thebenheckshow/187-teensy-tinball-portable/pics/IMG_20150423_170455569.jpg

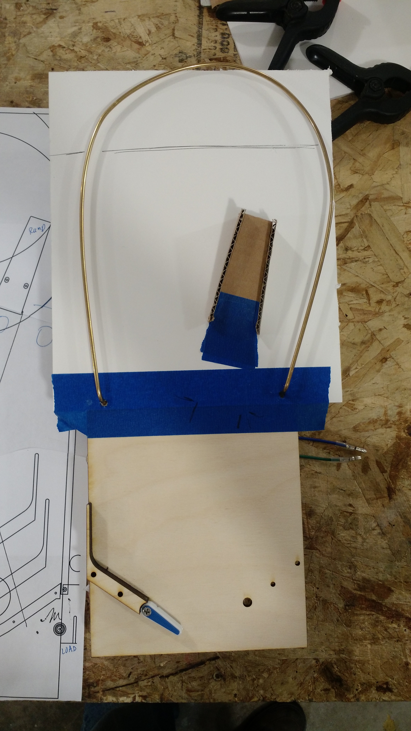
pics/IMG_20150423_170455569.jpg
