thebenheckshow/187-teensy-tinball-portable/pics/IMG_20150505_093643514.jpg

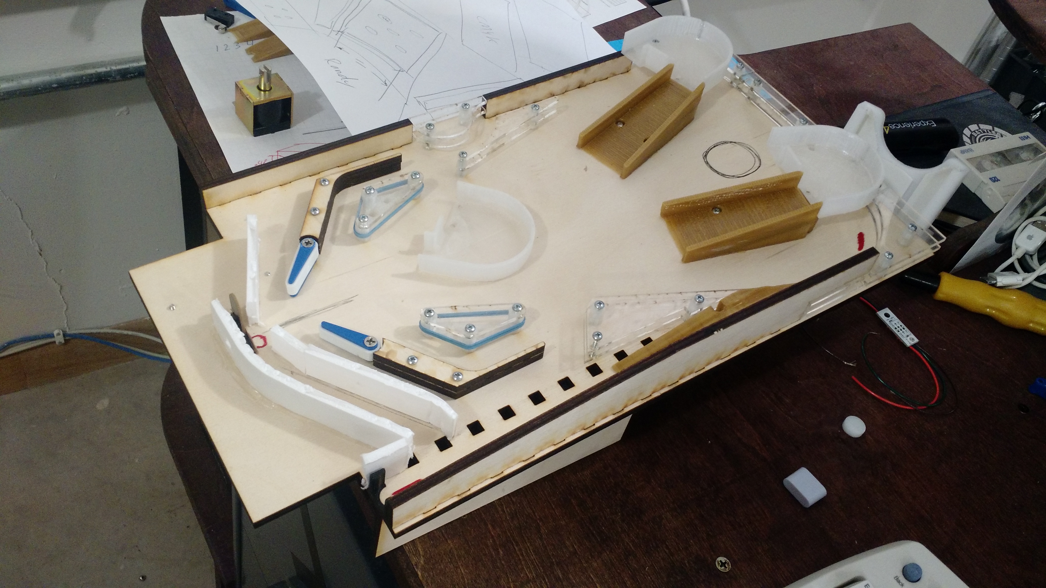
pics/IMG_20150505_093643514.jpg
