thebenheckshow/187-teensy-tinball-portable/pics/IMG_20150505_152138427.jpg

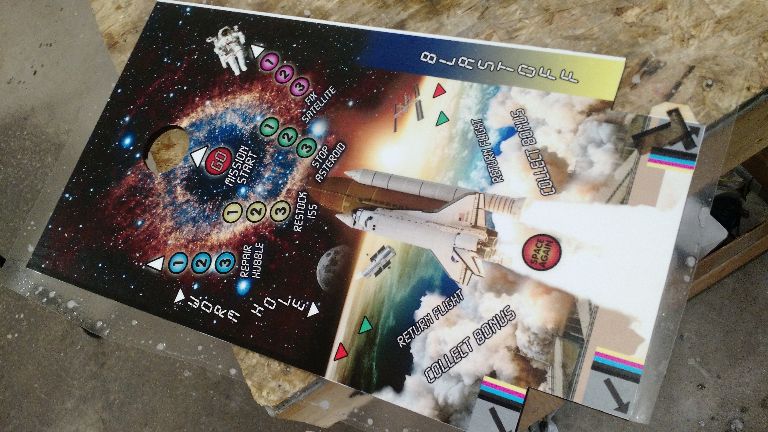
pics/IMG_20150505_152138427.jpg
