thebenheckshow/187-teensy-tinball-portable/pics/IMG_20150508_121546331.jpg

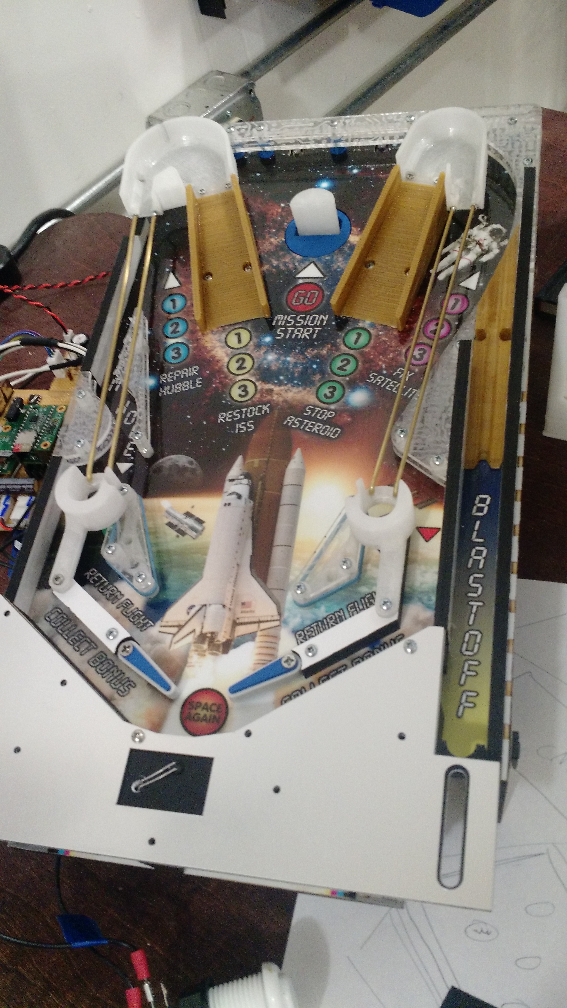
pics/IMG_20150508_121546331.jpg
