thebenheckshow/187-teensy-tinball-portable/pics/IMG_20150509_205021289.jpg

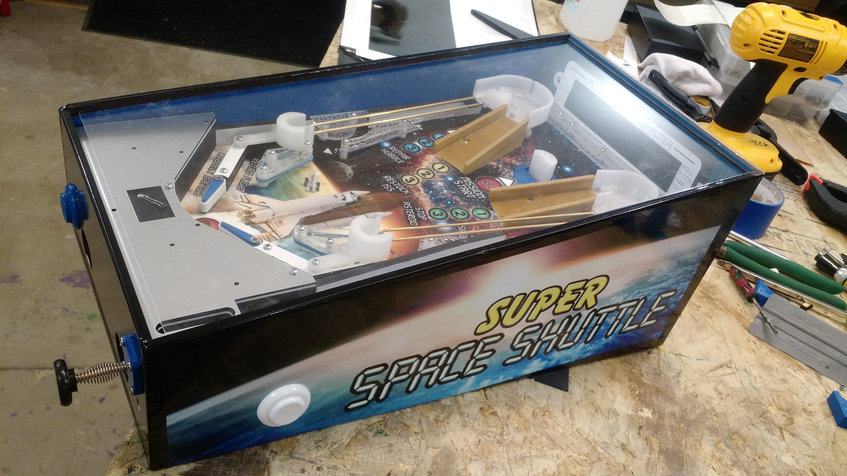
pics/IMG_20150509_205021289.jpg
