thebenheckshow/187-teensy-tinball-portable/pics/IMG_20150717_111414935.jpg

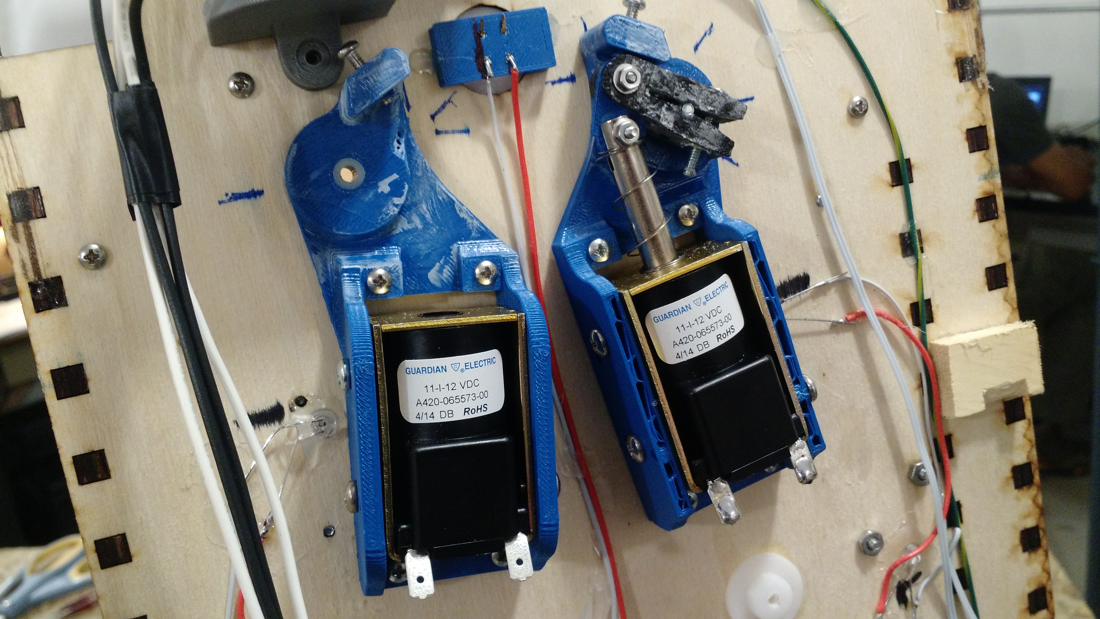
pics/IMG_20150717_111414935.jpg
