thebenheckshow/187-teensy-tinball-portable/3D parts/STL/Drop Target.stl

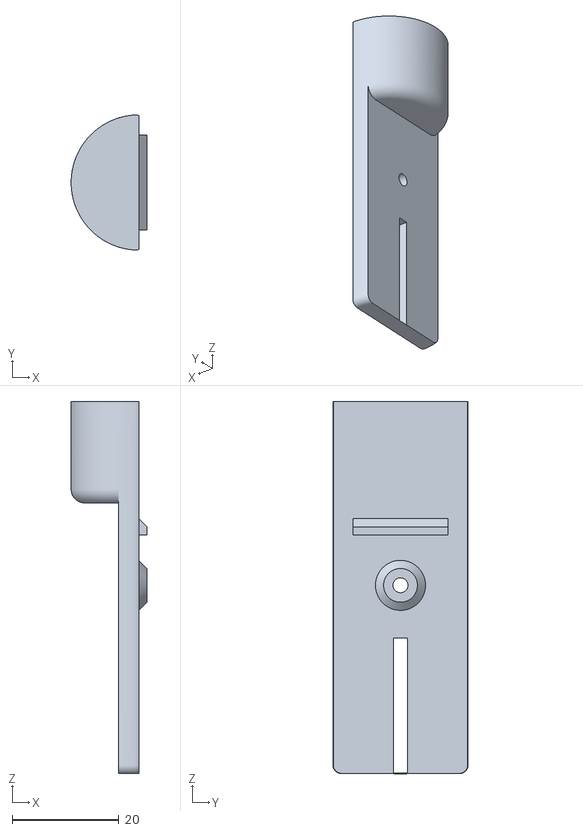
[picture p24: CAD file, 2015-11-03]
3D parts/STL/Drop Target.stl
14.2 x 25.4 x 69.8
