thebenheckshow/187-teensy-tinball-portable/3D parts/STL/Opto Mount 2.stl

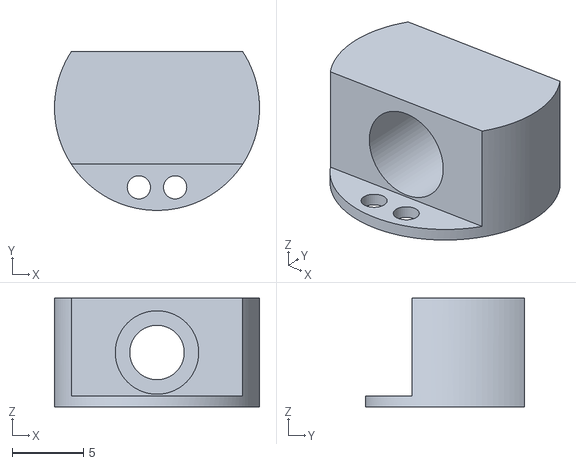
[picture p25: CAD file, 2015-11-03]
3D parts/STL/Opto Mount 2.stl
14.3 x 11.1 x 7.62
