thebenheckshow/187-teensy-tinball-portable/3D parts/STL/Shooter Tip.stl

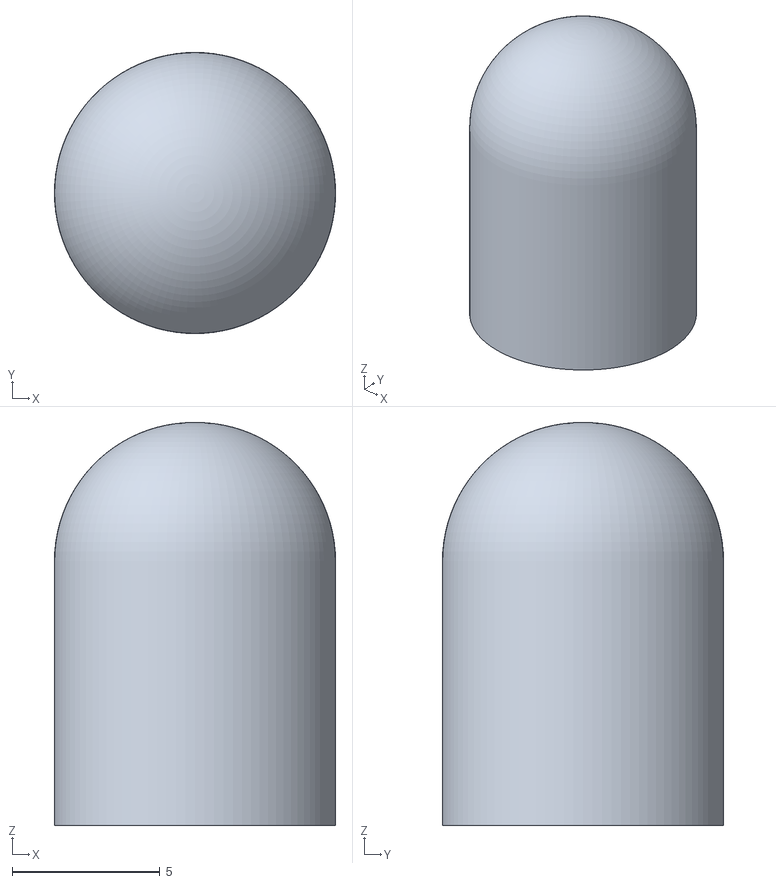
[picture p26: CAD file, 2015-11-03]
3D parts/STL/Shooter Tip.stl
9.53 x 9.53 x 13.7
