thebenheckshow/187-teensy-tinball-portable/3D parts/STL/Large LED holder.stl

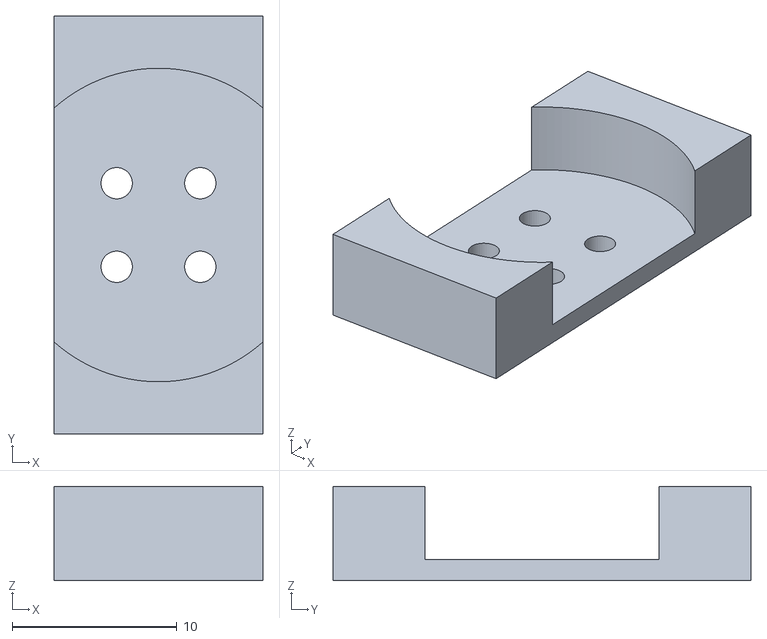
[picture p27: CAD file, 2015-11-03]
3D parts/STL/Large LED holder.stl
12.7 x 25.4 x 5.71
