thebenheckshow/187-teensy-tinball-portable/3D parts/STL/Foot.stl

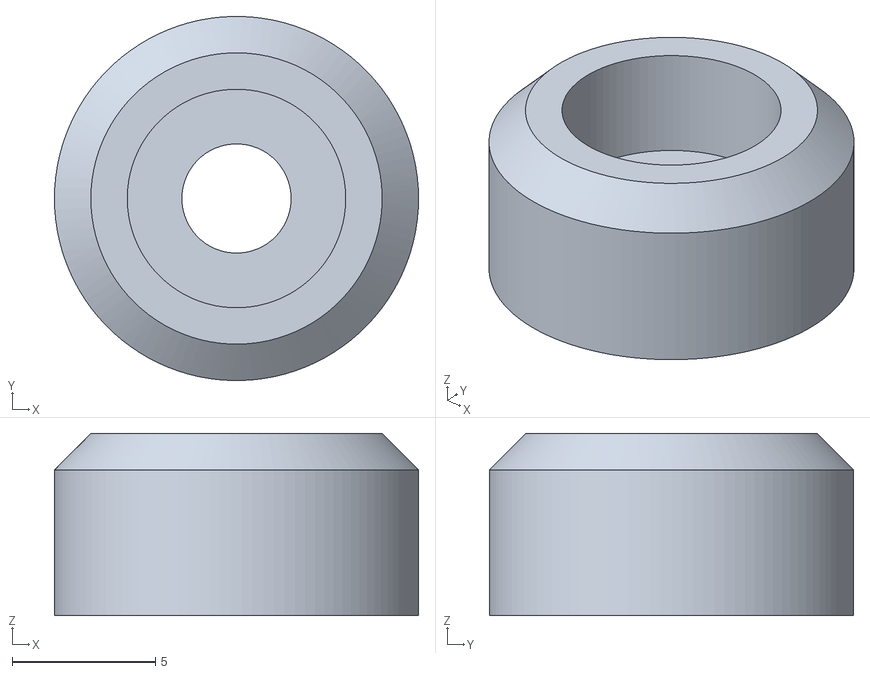
[picture p28: CAD file, 2015-11-03]
3D parts/STL/Foot.stl
12.7 x 12.7 x 6.35
