thebenheckshow/187-teensy-tinball-portable/3D parts/STL/Stop Cap 2.stl

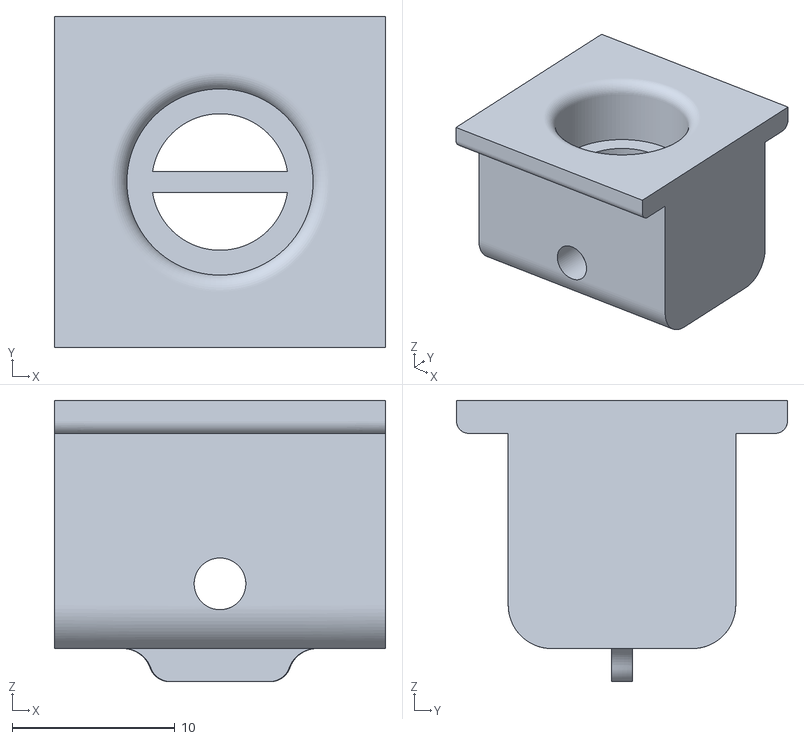
[picture p29: CAD file, 2015-11-03]
3D parts/STL/Stop Cap 2.stl
20.3 x 20.3 x 17.3
