thebenheckshow/187-teensy-tinball-portable/3D parts/STL/New Flipper Clamp Flipped.stl

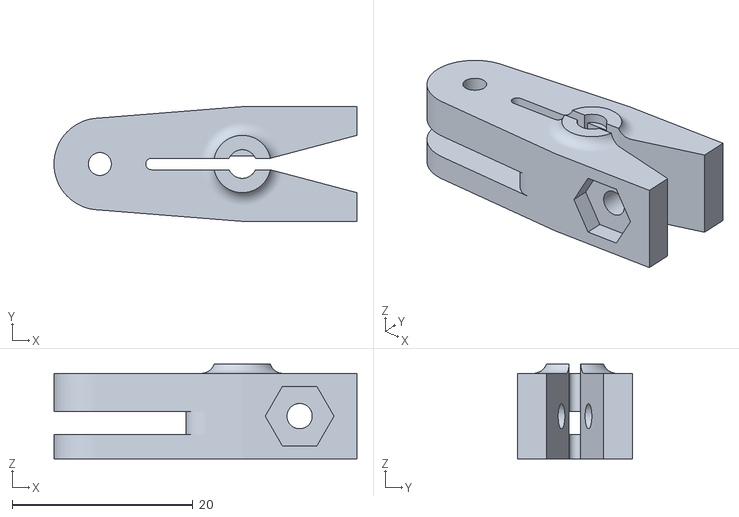
[picture p30: CAD file, 2015-11-03]
3D parts/STL/New Flipper Clamp Flipped.stl
33.5 x 12.7 x 10.5
