thebenheckshow/187-teensy-tinball-portable/3D parts/STL/Sling Mount R.stl

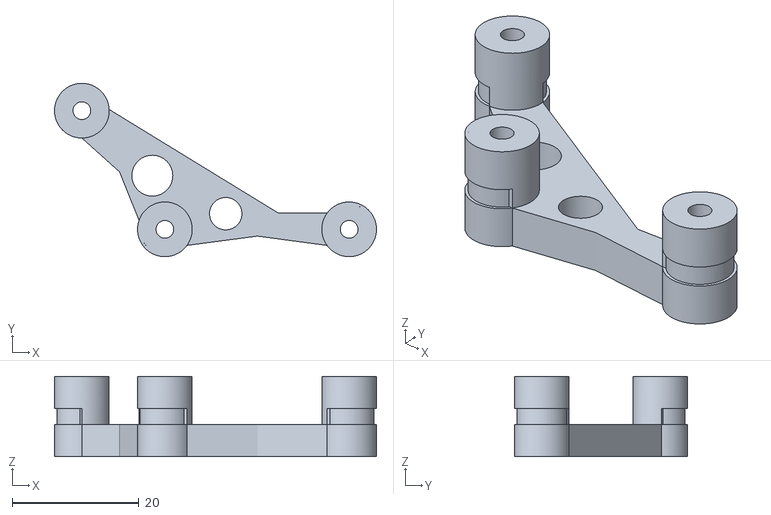
[picture p31: CAD file, 2015-11-03]
3D parts/STL/Sling Mount R.stl
50.8 x 27.4 x 12.7
