thebenheckshow/187-teensy-tinball-portable/3D parts/STL/Plastic Spacer 200 mils.stl

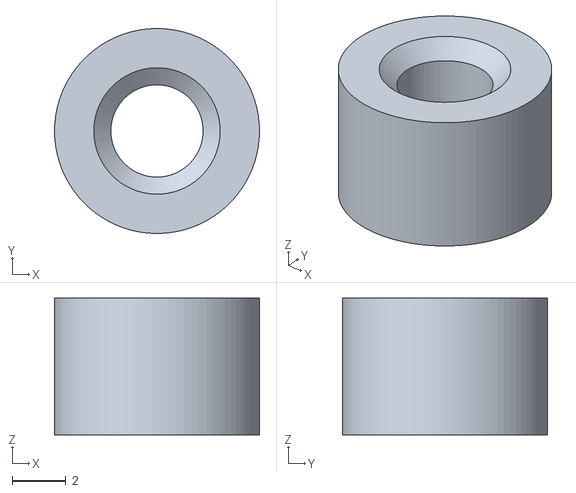
[picture p32: CAD file, 2015-11-03]
3D parts/STL/Plastic Spacer 200 mils.stl
7.62 x 7.61 x 5.08
