thebenheckshow/187-teensy-tinball-portable/3D parts/STL/Opto Mount.stl

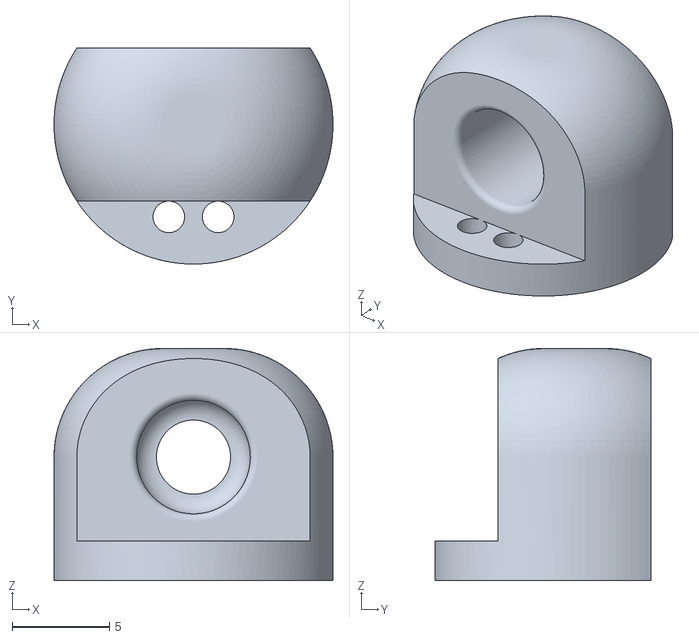
[picture p33: CAD file, 2015-11-03]
3D parts/STL/Opto Mount.stl
14.3 x 11.1 x 11.9
