thebenheckshow/187-teensy-tinball-portable/3D parts/STL/Habitrail End 2.stl

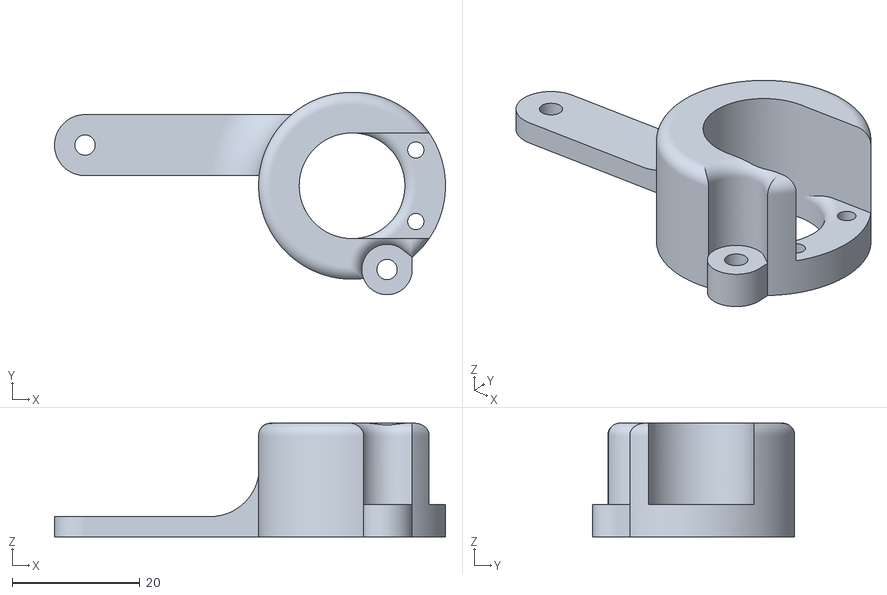
[picture p34: CAD file, 2015-11-03]
3D parts/STL/Habitrail End 2.stl
61.1 x 31.6 x 17.8
