thebenheckshow/187-teensy-tinball-portable/3D parts/STL/Target Slide Frame.stl

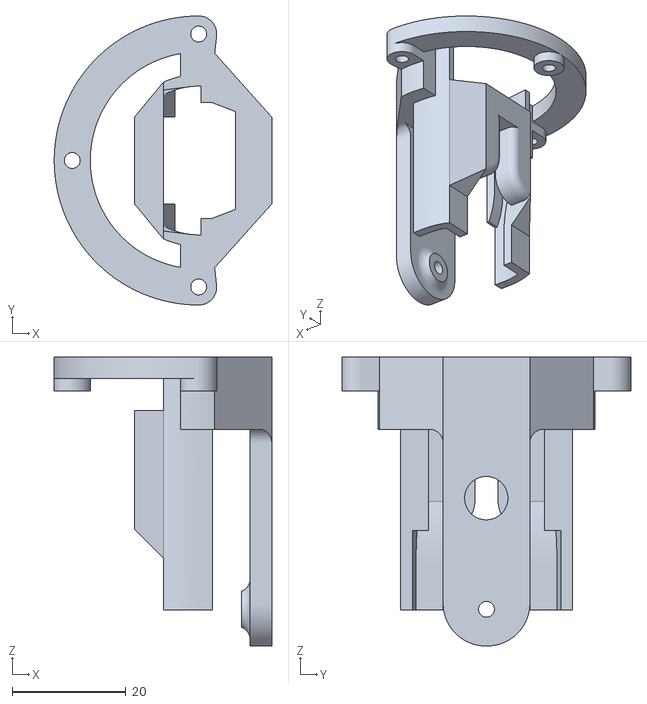
[picture p35: CAD file, 2015-11-03]
3D parts/STL/Target Slide Frame.stl
38.3 x 50.8 x 50.8
