thebenheckshow/187-teensy-tinball-portable/3D parts/STL/Hole Temp.stl

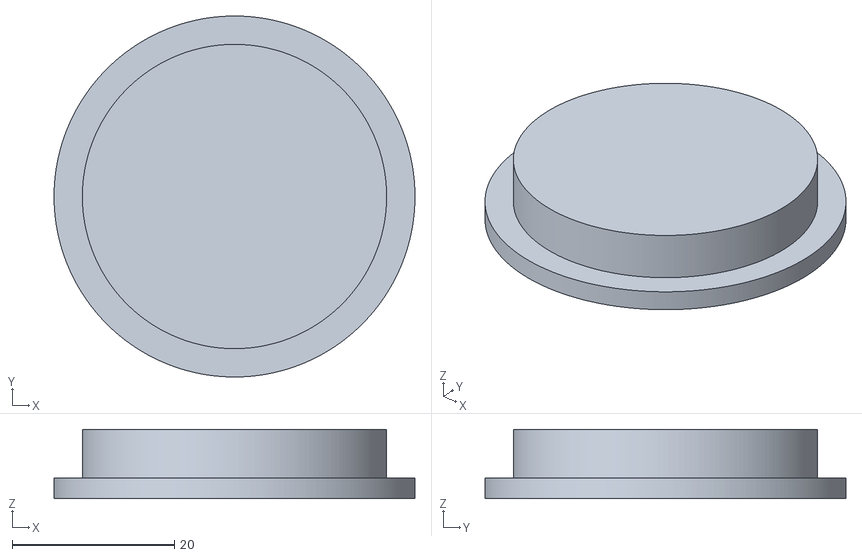
[picture p36: CAD file, 2015-11-03]
3D parts/STL/Hole Temp.stl
44.4 x 44.4 x 8.54
