thebenheckshow/187-teensy-tinball-portable/3D parts/STL/Top Holder Right.stl

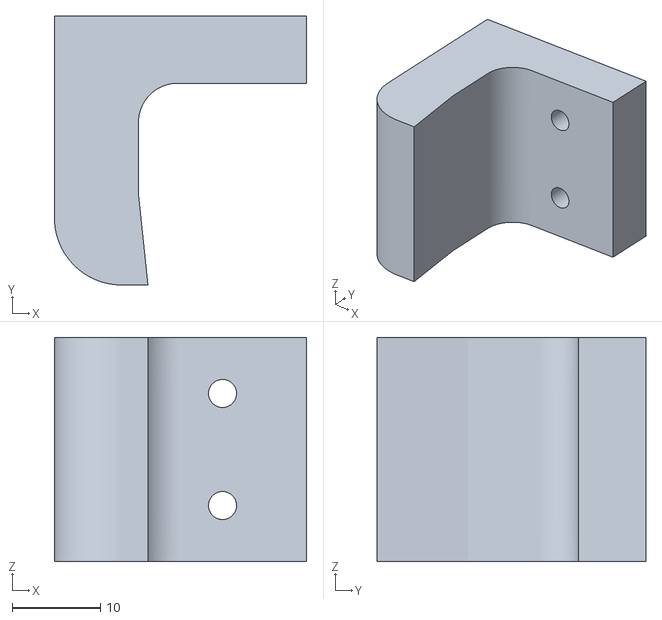
[picture p37: CAD file, 2015-11-03]
3D parts/STL/Top Holder Right.stl
28.6 x 30.5 x 25.4
