thebenheckshow/187-teensy-tinball-portable/3D parts/STL/Left Ramp Loop.stl

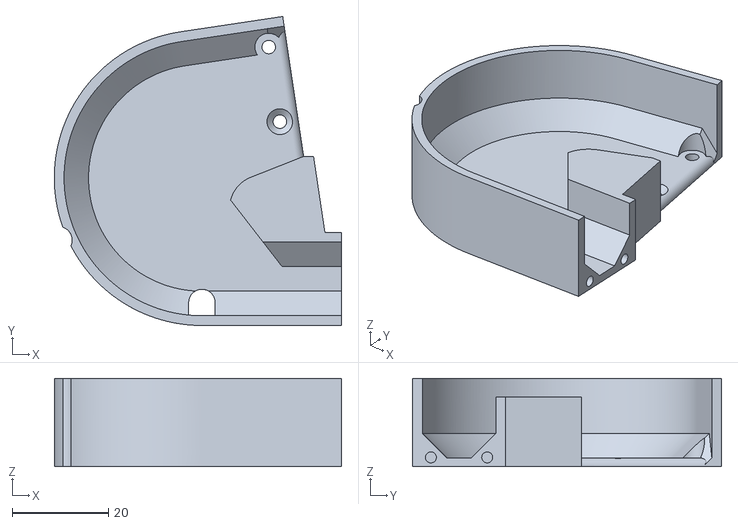
[picture p38: CAD file, 2015-11-03]
3D parts/STL/Left Ramp Loop.stl
59.6 x 64.1 x 18.3
