thebenheckshow/187-teensy-tinball-portable/3D parts/STL/Flipper Bat.stl

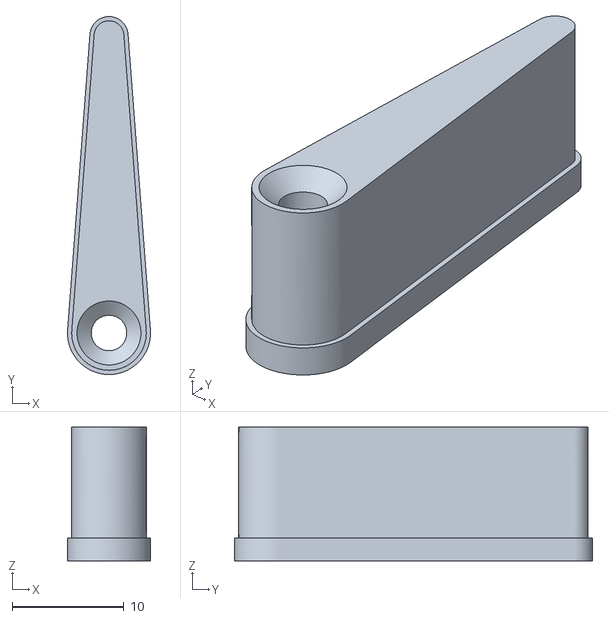
[picture p39: CAD file, 2015-11-03]
3D parts/STL/Flipper Bat.stl
7.43 x 32.0 x 11.9
