thebenheckshow/187-teensy-tinball-portable/3D parts/STL/LED holder.stl

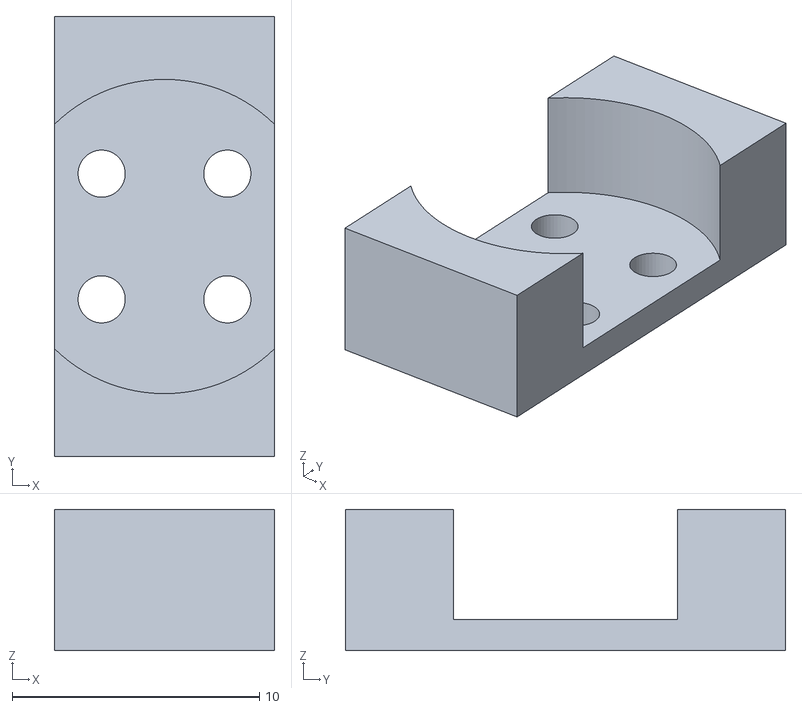
[picture p40: CAD file, 2015-11-03]
3D parts/STL/LED holder.stl
8.89 x 17.8 x 5.71
