thebenheckshow/187-teensy-tinball-portable/3D parts/STL/Shooter Rod Mount.stl

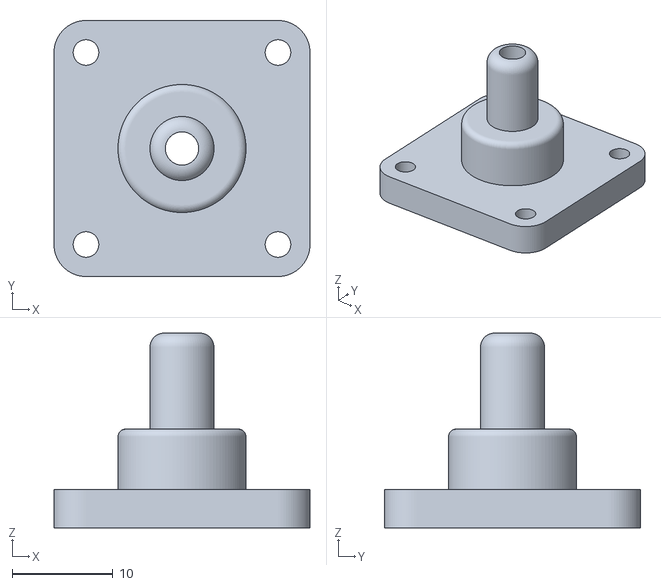
[picture p41: CAD file, 2015-11-03]
3D parts/STL/Shooter Rod Mount.stl
25.4 x 25.4 x 19.3
