thebenheckshow/187-teensy-tinball-portable/3D parts/STL/glass knob.stl

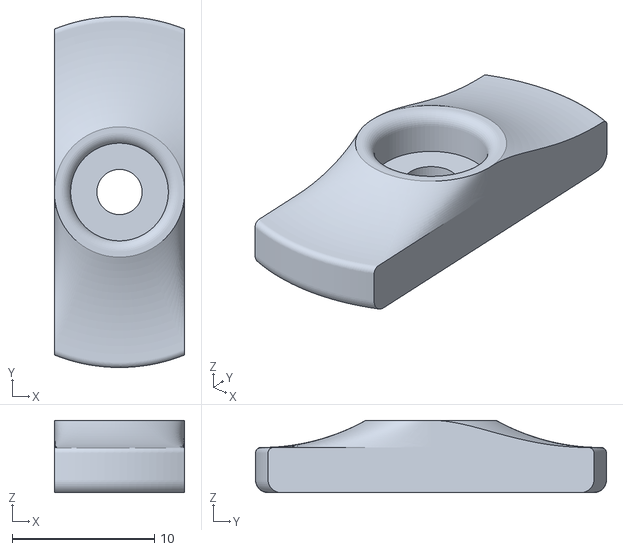
[picture p42: CAD file, 2015-11-03]
3D parts/STL/glass knob.stl
9.14 x 24.6 x 5.08
