thebenheckshow/187-teensy-tinball-portable/3D parts/STL/Shooter Rod Mount 2.stl

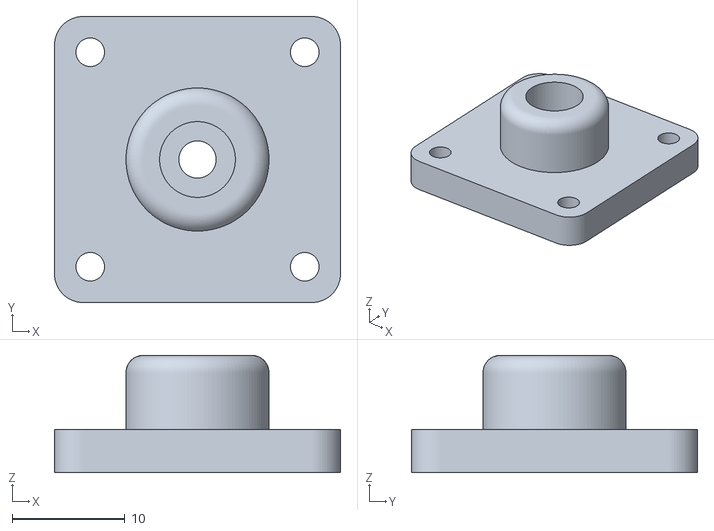
[picture p43: CAD file, 2015-11-03]
3D parts/STL/Shooter Rod Mount 2.stl
25.4 x 25.4 x 10.4
