thebenheckshow/187-teensy-tinball-portable/3D parts/STL/Top Holders.stl

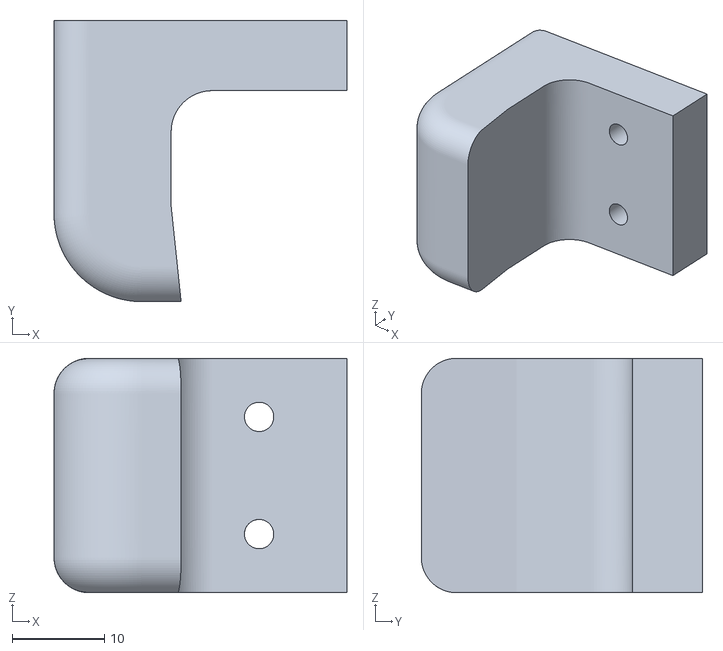
[picture p44: CAD file, 2015-11-03]
3D parts/STL/Top Holders.stl
31.8 x 30.5 x 25.4
