thebenheckshow/187-teensy-tinball-portable/3D parts/STL/Launch Ramp.stl

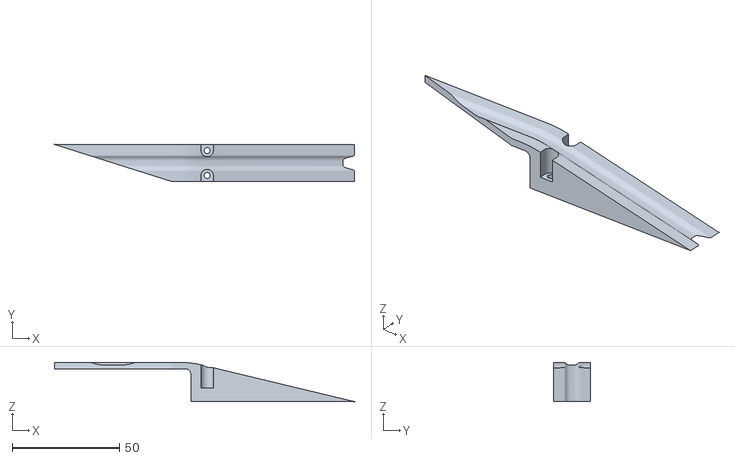
[picture p45: CAD file, 2015-11-03]
3D parts/STL/Launch Ramp.stl
139.7 x 17.3 x 18.3
