thebenheckshow/187-teensy-tinball-portable/3D parts/STL/New Flipper Linkage.stl

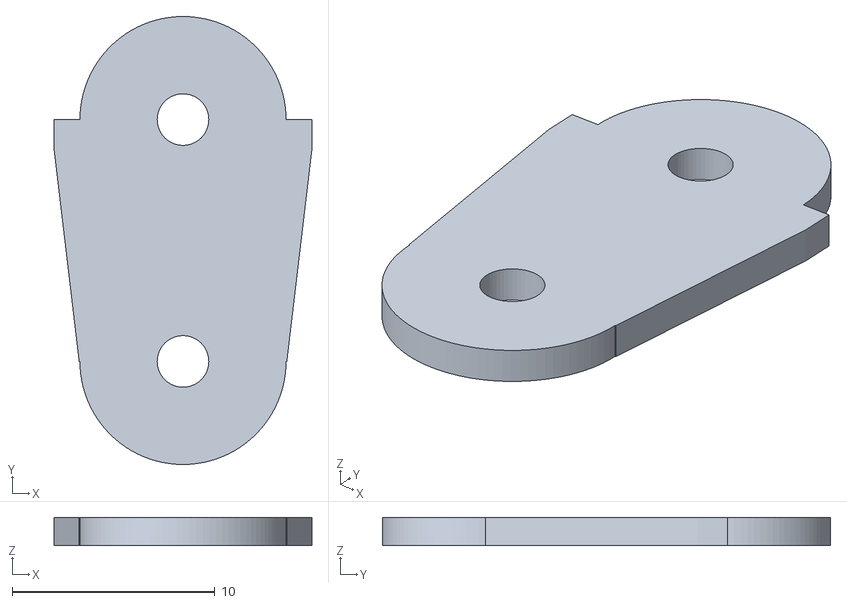
[picture p46: CAD file, 2015-11-03]
3D parts/STL/New Flipper Linkage.stl
12.7 x 22.1 x 1.40
