thebenheckshow/187-teensy-tinball-portable/3D parts/STL/Super Triangle.stl

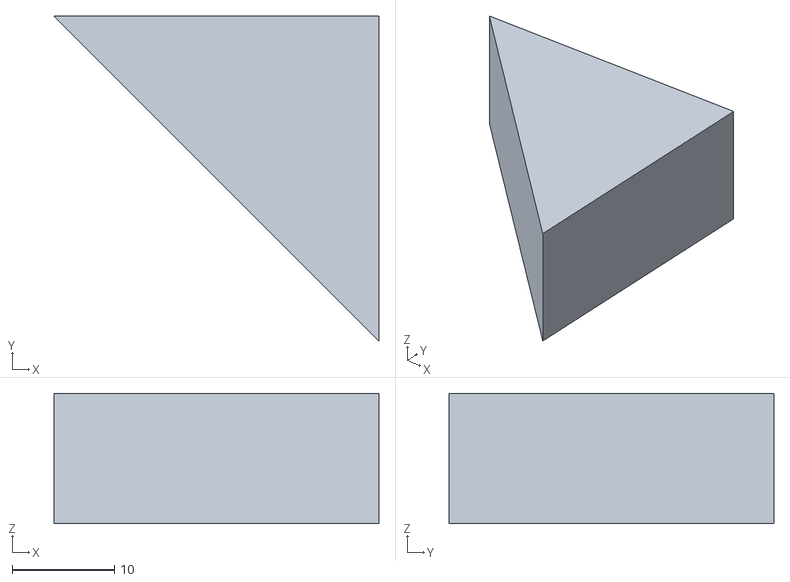
[picture p47: CAD file, 2015-11-03]
3D parts/STL/Super Triangle.stl
31.7 x 31.7 x 12.7
