thebenheckshow/187-teensy-tinball-portable/3D parts/STL/Sling Coil Mount.stl

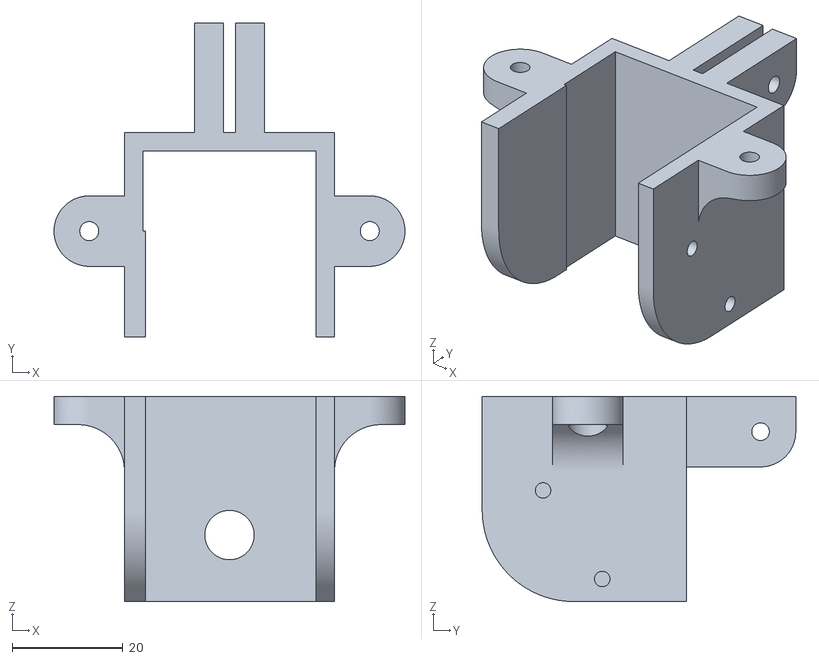
[picture p48: CAD file, 2015-11-03]
3D parts/STL/Sling Coil Mount.stl
63.3 x 56.5 x 37.0
