thebenheckshow/187-teensy-tinball-portable/3D parts/STL/pf flange.stl

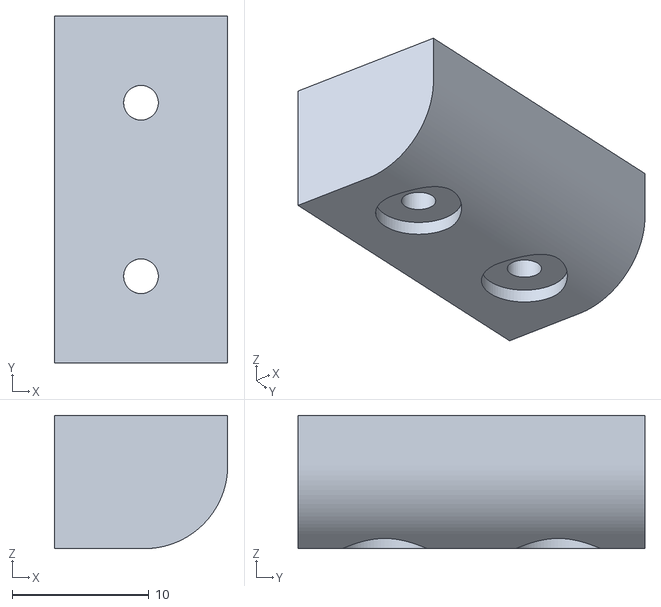
[picture p49: CAD file, 2015-11-03]
3D parts/STL/pf flange.stl
12.7 x 25.4 x 9.76
