thebenheckshow/187-teensy-tinball-portable/3D parts/STL/Right Ramp Loop.stl

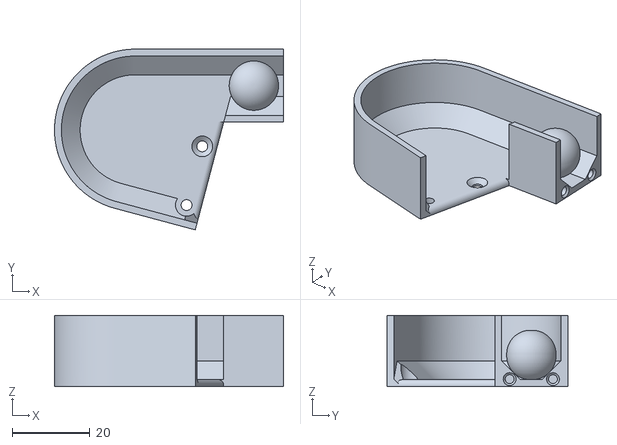
[picture p50: CAD file, 2015-11-03]
3D parts/STL/Right Ramp Loop.stl
58.9 x 46.5 x 18.3
