thebenheckshow/187-teensy-tinball-portable/3D parts/STL/rotate mount.stl

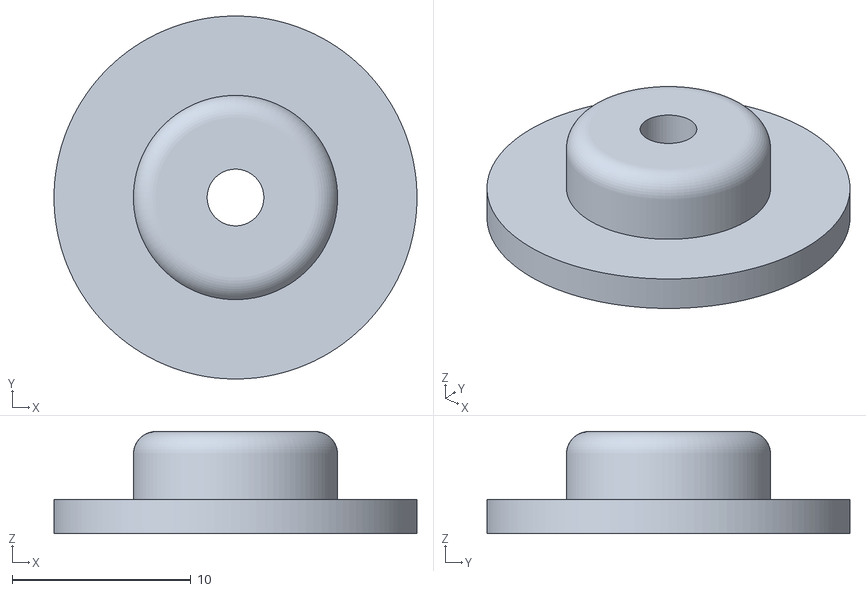
[picture p51: CAD file, 2015-11-03]
3D parts/STL/rotate mount.stl
20.3 x 20.3 x 5.71
