thebenheckshow/187-teensy-tinball-portable/3D parts/STL/Taller Rubber.stl

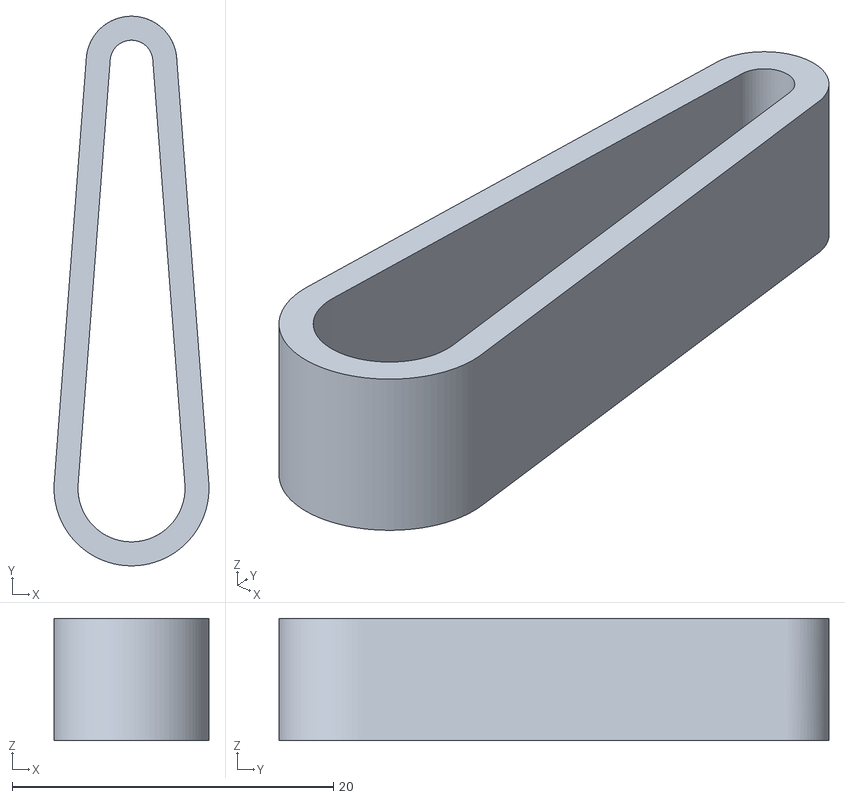
[picture p52: CAD file, 2015-11-03]
3D parts/STL/Taller Rubber.stl
9.65 x 34.2 x 7.62
