thebenheckshow/187-teensy-tinball-portable/3D parts/STL/Knob.stl

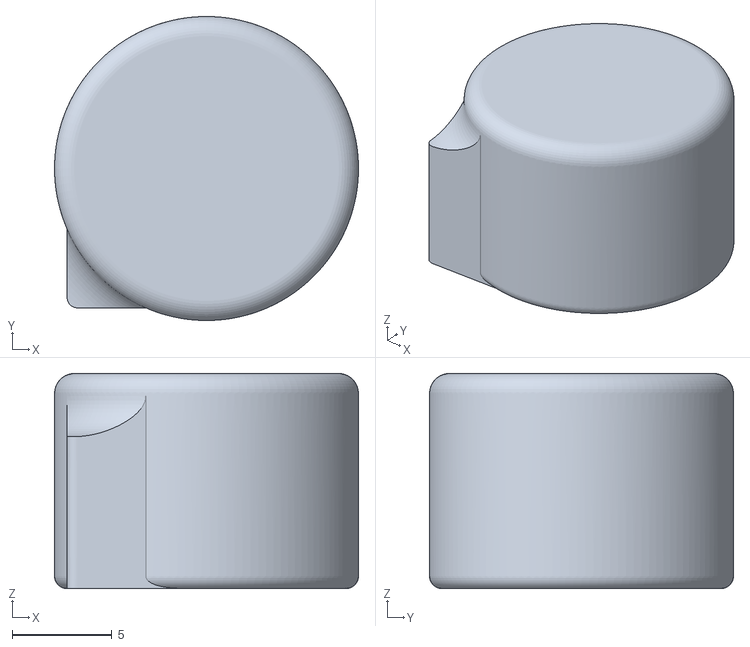
[picture p53: CAD file, 2015-11-03]
3D parts/STL/Knob.stl
15.2 x 15.2 x 10.8
