thebenheckshow/187-teensy-tinball-portable/3D parts/STL/Habitrail Top.stl

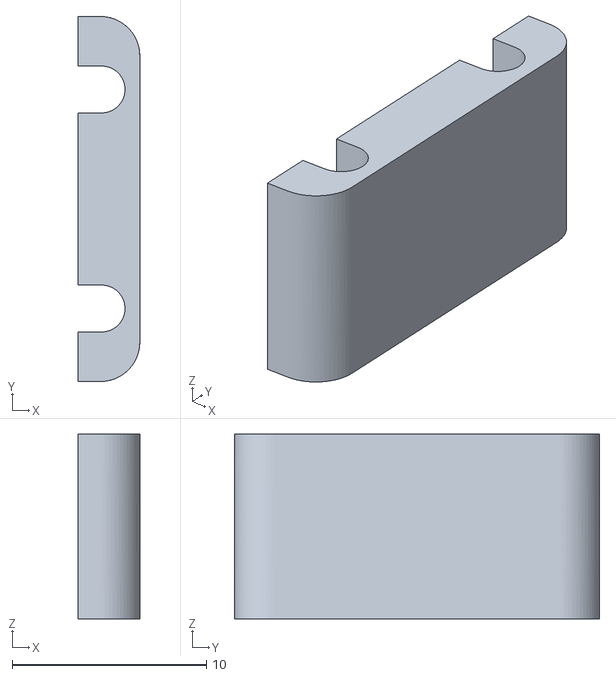
[picture p54: CAD file, 2015-11-03]
3D parts/STL/Habitrail Top.stl
3.17 x 18.8 x 9.53
