thebenheckshow/187-teensy-tinball-portable/3D parts/STL/Plastic Spacer 200 mils THEEEN.stl

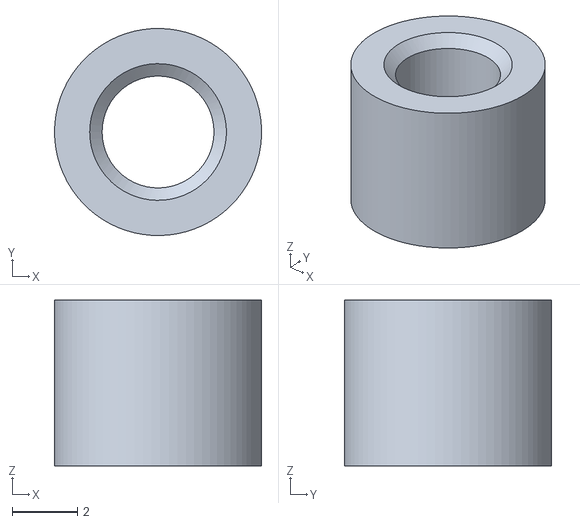
[picture p55: CAD file, 2015-11-03]
3D parts/STL/Plastic Spacer 200 mils THEEEN.stl
6.35 x 6.35 x 5.08
